Sheepy3/Sheepypad/circuitpython/boot.py

# This example is for the MacroPad,
# or any board with buttons that are connected to ground when pressed.

import storage
import board, digitalio

# On the Macropad, pressing a key grounds it. You need to set a pull-up.
# If not pressed, the key will be at +V (due to the pull-up).
button = digitalio.DigitalInOut(board.GP16)
button.pull = digitalio.Pull.UP

# Disable devices only if button is not pressed.
if button.value:
   storage.disable_usb_drive()
